yazidta/Flying-Probe-Tester/STM32/Components/Inc/encoder_config.h

/*
 * encoder_config.h
 *
 *  Created on: Nov 28, 2024
 *      Author: yazed
 */
/* Includes ------------------------------------------------------------------*/
#ifndef INC_ENCODER_CONFIG_H_
#define INC_ENCODER_CONFIG_H_

/* Config --------------------------------------------------------------------*/

/* Includes ------------------------------------------------------------------*/
#include "encoder.h"

/* Typedef -------------------------------------------------------------------*/

/* Define --------------------------------------------------------------------*/
extern TIM_HandleTypeDef htim4;
;

/* Macro ---------------------------------------------------------------------*/

/* Public variables ----------------------------------------------------------*/
extern ENC_Handle_TypeDef henc1;

/* Public function prototypes ------------------------------------------------*/

#endif /* INC_ENCODER_CONFIG_H_ */
