yazidta/Flying-Probe-Tester/STM32/Components/Inc/TMC2209.h

/******************************************************************************
 * @file       TMC2209.cpp
 * @author     Ahmed Bouras
 * @date       05/12/2024
 * @version    0.6
 *
 * @copyright  Copyright (c) [2024] Ahmed Bouras
 *
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
 * @note       This library provides an interface for controlling the TMC2209
 *             stepper motor driver over STEP, DIR, ENN & UART.
 ******************************************************************************
 */

#ifndef TMC2209_H
#define TMC2209_H

#include "stm32f7xx_hal.h"
#include "TMC2209_configs.h"
#include "TMC2209_register.h"
#include "extras.h"
#include "main.h"
#include "uart_handler.h"
#include <stdio.h>
#include <stdlib.h>
#include <string.h>
#include <stdbool.h>





// Datagrams
#define TMC_WRITE_DATAGRAM_SIZE  		8
#define TMC_READ_REQUEST_DATAGRAM_SIZE  4

// Macros & other
#define ENABLE_DEBUG					0		// If this is set to 1 then UART debug will be enabled
#define SYNC 							0x05     // Sync byte value for communication
#define SENDDELAY_MULTIPLIER 			8 		// 8-bit times per SENDDELAY unit
#define BAUD_RATE 						115200
#define TMC_ERROR						-1
#define TMC_ENABLESTALL_ERROR			10
#define TMC_STALL_ERROR					15
#define TMC_SEND_ERROR					20
#define TMC_NOREPLY_ERROR				30
#define TMC_SYNC_REPLY_ERROR			40
#define TMC_MCU_REPLY_ERROR				50
#define TMC_REG_REPLY_ERROR				60
#define TMC_CRC_REPLY_ERROR				70
#define TMC_IFCNT_ERROR					-80
#define TMC_GCONF_ERROR					90
#define TMC_IHOLD_ERROR					91
#define TMC_IRUN_ERROR					92
#define TMC_IDELAY_ERROR				93
#define TMC_SPREADCYCLE_ERROR1			95
#define TMC_SPREADCYCLE_ERROR2			100
#define TMC_SET_SPREADCYCLE_ERROR		105
#define TMC_SET_MSTEP_ERROR				110
#define TMC2209_IRUN_ERROR				120
#define TMC2209_SENDELAY_ERROR			130
#define TMC2209_TCOOLTHRS_ERROR			-10

#define TMC_OK							0






// Variables

extern uint32_t last_tmc_read_attempt_ms;
extern Axis axes[MAX_MOTORS_PER_AXIS];

// Function prototypes

void TMC2209_SetDirection(Motor *motor, GPIO_PinState state);
void TMC2209_EnableDriver(Motor *motor, GPIO_PinState state);
uint8_t TMC2209_ReadDiag(Motor *motor);
uint32_t TMC2209_ReadIndexStatus(Motor *motor);
void TMC2209_SetSpeed(Motor *motor, uint32_t StepFrequency);
void TMC2209_Step(Motor *motor, uint32_t steps);
void TMC2209_Stop(Motor *motor);
void TMC2209_Start(Motor *motor);
void TMC2209_checkStatus(Motor *motor, bool *isStepping, uint32_t *nextTotalSteps);
void TMC2209_MoveTo(Axis *axis, uint8_t motorIndex, float targetPositionMM);

uint8_t getStepPerUnit(Motor *motor);

//// UART TMC2209 ////
uint8_t calculate_CRC(uint8_t *datagram, uint8_t length);
uint8_t *TMC2209_sendCommand(uint8_t *command, size_t writeLength, size_t readLength, Motor *tmc2209);
void TMC2209_writeInit(Motor *tmc2209, uint8_t regAddress, int32_t value);
int32_t TMC2209_readInit(Motor *tmc2209, uint8_t regAddress);
uint8_t TMC2209_waitForReply(uint32_t timeout);

//// TMC2209 configuration functions (UART)  ////
bool TMC2209_setPDNuart(Motor *tmc2209, bool enable);
bool configureGCONF(Motor *tmc2209);
void TMC2209_read_ifcnt(Motor *tmc2209);
float TMC2209_readTemperature(Motor *tmc2209);
uint8_t TMC2209_enableStallDetection(Motor *tmc2209, uint8_t sgthrs);
void TMC2209_checkStall(Motor *tmc2209);
bool TMC2209_readStandstillIndicator(Motor *tmc2209);

uint32_t TMC2209_setMicrosteppingResolution(Motor *tmc2209, uint16_t resolution);
void checkMicrosteppingResolution(Motor *tmc2209);
uint16_t TMC2209_setSpreadCycle(Motor *motor, uint8_t enable);
void checkSpreadCycle(Motor *tmc2209);
uint16_t TMC2209_setIRUN(Motor *tmc2209, uint8_t irun_value);
void TMC2209_readIRUN(Motor *tmc2209);
void TMC2209_configureCurrent(Motor *tmc2209, uint8_t ihold, uint8_t irun, uint8_t iholddelay);
void TMC2209_SetTCoolThrs(Motor *tmc2209, uint32_t stepFrequency);

void TMC2209_setMotorsConfiguration(Motor *motors);
void TMC2209_resetMotorsConfiguration(Motor *motors);



//// Debug ////
void debug_print(const char* msg);
void debug_print_hex(uint8_t* data, uint8_t length);
void clear_UART_buffers(UART_HandleTypeDef *huart);
void TMC2209_MoveAllMotorsTo(Axis axes[2], float targetPositions[4]);



#endif // TMC2209_H
