yazidta/Flying-Probe-Tester/STM32/Components/Inc/LCD.h

#ifndef INC_LCD_H_
#define INC_LCD_H_

/* Config --------------------------------------------------------------------*/
#define LCD_PRINTF_ENABLE
#define LCD_USE_TIMER
#define MAX_LINES       500    // Maximum number of lines to process
#define LINE_BUFFER_SIZE 500
#define MAX_LINE_LENGTH 64
//#define LCD20xN    // For 20xN LCDs
#define LCD16xN     // For 16xN LCDs

#ifdef LCD16xN
#define LCD_LINE_LEN 16
#define LCD_LINE_BUF_LEN 17
#else
#define LCD_LINE_LEN 20
#define LCD_LINE_BUF_LEN 21
#endif
extern char lines[MAX_LINES][MAX_LINE_LENGTH];


/* Includes ------------------------------------------------------------------*/

#include <string.h>
#include <stdio.h>
#include "stm32f7xx_hal.h"
#include "encoder.h"
#include <stdbool.h>
#include "stm32f7xx_hal_tim.h"
#include "main.h"
#include "stm32f7xx_hal_conf.h"
#include <stdarg.h>
#include "sd_card_reader.h"
//#include "calibration.h"
/* Typedef -------------------------------------------------------------------*/
#define LCD_TimerType TIM_HandleTypeDef*

#define LCD_I2CType I2C_HandleTypeDef*

typedef struct {
  LCD_I2CType I2C;
  uint16_t Address;
  uint32_t Timeout;
  //LCD_ModeTypeDef Mode;
  LCD_TimerType Timer;
  _Bool IsInitialized;
} LCD_I2C_HandleTypeDef;

/* Define --------------------------------------------------------------------*/

#define LCD_CLEAR_DISPLAY 0x01

#define LCD_RETURN_HOME 0x02

#define LCD_ENTRY_MODE_SET 0x04
#define LCD_OPT_S   0x01        // Shift entire display to right
#define LCD_OPT_INC 0x02        // Cursor increment

#define LCD_DISPLAY_ON_OFF_CONTROL 0x08
#define LCD_OPT_D  0x04         // Turn on display
#define LCD_OPT_C  0x02         // Turn on cursor
#define LCD_OPT_B  0x01         // Turn on cursor blink

#define LCD_CURSOR_DISPLAY_SHIFT 0x10 // Move and shift cursor
#define LCD_OPT_SC 0x08
#define LCD_OPT_RL 0x04

#define LCD_FUNCTION_SET    0x20
#define LCD_OPT_DL          0x10    // Set interface data length
#define LCD_OPT_N           0x08    // Set number of display lines
#define LCD_OPT_F           0x04    // Set alternate font
#define LCD_SETCGRAM_ADDR  0x040
#define LCD_SET_DDRAM_ADDR  0x80    // Set DDRAM address

#define LCD_NIB  4
#define LCD_BYTE 8

#define LCD_DATA_REG    1
#define LCD_COMMAND_REG 0

#define LCD_MENU_CURSOR_CHAR 0x7E // '->' (ROM Code: A00)
#define LCD_I2C_BIT_RS                 0x01
#define LCD_I2C_BIT_RW                 0x02
#define LCD_I2C_BIT_E                  0x04
#define LCD_I2C_BIT_BACKIGHT_ON        0x08
#define LCD_I2C_BIT_BACKIGHT_OFF       0x00
#define MAX_FILES 10
#define LCD_ROWS 4
//#define LCD_WIDTH 20

/**
 * @brief LCD initialization procedure.
 * @note Cursor off, Cursor increment on, No blink @see HD44780 technical note.
 * @param[in] hlcd : LCD handler with I2C interface
 * @return None
 */
void LCD_I2C_Init(LCD_I2C_HandleTypeDef* hlcd);

/**
 * @brief Write a decimal number on the current position.
 * @param[in] hlcd   : LCD handler with I2C interface
 * @param[in] number : Decimal number
 * @return None
 */
void LCD_I2C_printDecInt(LCD_I2C_HandleTypeDef* hlcd, int number);

/**
 * @brief Write a hexadecimal number on the current position.
 * @param[in] hlcd   : LCD handler with I2C interface
 * @param[in] number : Hexadecimal number
 * @return None
 */
void LCD_I2C_printHexInt(LCD_I2C_HandleTypeDef* hlcd, int number);

/**
 * @brief Write a string on the current position.
 * @param[in] hlcd : LCD handler with I2C interface
 * @param[in] str  : Null-terminated string
 * @return None
 */
void LCD_I2C_printStr(LCD_I2C_HandleTypeDef* hlcd, char* str);

/**
 * @brief Set the cursor position.
 * @param[in] hlcd : LCD handler with I2C interface
 * @param[in] row  : Display row (line): 0 to N
 * @param[in] col  : Display column: 0 to 15 (16 character display) or 19 (20 character display)
 * @return None
 */
void LCD_I2C_SetCursor(LCD_I2C_HandleTypeDef* hlcd, uint8_t row, uint8_t col);

/**
 * @brief Clear the screen.
 * @param[in] hlcd : LCD handler with I2C interface
 * @return None
 */
void LCD_I2C_Clear(LCD_I2C_HandleTypeDef * lcd);

/**
 * @brief Write new character to display memory.
 * @param[in] hlcd   : LCD handler with I2C interface
 * @param[in] code   : Defined character code in display memory @see HD44780 technical note.
 * @param[in] bitmap : Defined character array @see HD44780 technical note.
 * @return None
 */
void LCD_I2C_DefineChar(LCD_I2C_HandleTypeDef* lcd, uint8_t code, uint8_t bitmap[]);

#ifdef LCD_PRINTF_ENABLE
/**
 * @brief Write text in standard format on the current position.
 * @param[in] hlcd   : LCD handler with I2C interface
 * @param[in] format : Text format @see http://www.cplusplus.com/reference/cstdio/printf/
 * @param[in] ...    : Variadic arguments
 * @return None
 */
void LCD_I2C_printf(LCD_I2C_HandleTypeDef* lcd, const char* format, ...);

void DisplaySequentialGlossyText(LCD_I2C_HandleTypeDef* hlcd, uint8_t row);
void DisplayGlossyText(LCD_I2C_HandleTypeDef* hlcd, uint8_t row);
void LCD_I2C_HandleMenuSelection(uint8_t selectedOption, LCD_I2C_HandleTypeDef* hlcd,ENC_Handle_TypeDef* henc);
void LCD_I2C_DisplayGlossyText(LCD_I2C_HandleTypeDef* hlcd, uint8_t row);
bool read_buttons(void);
uint8_t LCD_I2C_MainMenu_Encoder(LCD_I2C_HandleTypeDef* hlcd, ENC_Handle_TypeDef* henc);
void sd_card_display_files(LCD_I2C_HandleTypeDef* hlcd);
void LCD_I2C_DisplaySDMenu(LCD_I2C_HandleTypeDef* hlcd, ENC_Handle_TypeDef* henc);
void LCD_I2C_Cursor(LCD_I2C_HandleTypeDef* hlcd, uint8_t row, uint8_t col);
void DisplayMenu(LCD_I2C_HandleTypeDef* hlcd, char fileList[][20 + 1], uint8_t fileCount, uint8_t selectedIndex);
void AddBackOption(char fileList[][20 + 1], uint8_t index);
uint8_t LCD_I2C_menuTemplate(LCD_I2C_HandleTypeDef* hlcd,
                             ENC_Handle_TypeDef* henc,
                             const char* displayItems[],
                             uint8_t numItems,
                             bool backOption);
uint8_t ReadFiles(DIR* dir, char fileList[][20 + 1], uint8_t maxFiles);
FRESULT OpenRootDir(DIR* dir);
FRESULT MountSDCard(FATFS* FatFs);
void LCD_I2C_ClearAllLines(LCD_I2C_HandleTypeDef * hlcd);
void generate_report(LCD_I2C_HandleTypeDef* hlcd);



#endif

#endif /* INC_LCD_H_ */
