yazidta/Flying-Probe-Tester/STM32/Components/Inc/command_parser.h

/*
 * command_parser.h
 *
 *  Created on: Jan 16, 2025
 *      Author: ahmed
 */

#ifndef INC_COMMAND_PARSER_H_
#define INC_COMMAND_PARSER_H_

void parsePCB2GcodeCommand(char *command);

#endif /* INC_COMMAND_PARSER_H_ */
