yazidta/Flying-Probe-Tester/STM32/Components/Src/lcd_config.c

/**
  ******************************************************************************
  * @file    lcd_config.c
  * @author  Konrad Marchewka
  * @author   : AW    Adrian.Wojcik@put.poznan.pl
  * @version V1.0
  * @date    23-Jan-2024
  * @brief   Simple HD44780 driver library for STM32F7 configuration file.
  *
  ******************************************************************************
  */
  /* Private includes ----------------------------------------------------------*/

#include "LCD.h"
#include "lcd_config.h"
#include "main.h"
#include "stm32f7xx_hal_i2c.h"
#include "stm32f7xx_hal_tim.h"

//#include "i2c.h"
//#include "tim.h"

/* Private typedef -----------------------------------------------------------*/

/* Private define ------------------------------------------------------------*/
#ifdef LCD_USE_TIMER
#endif
/* Private macro -------------------------------------------------------------*/

/* Private variables ---------------------------------------------------------*/

/* Public variables ----------------------------------------------------------*/
extern I2C_HandleTypeDef hi2c1;
extern TIM_HandleTypeDef htim7;

LCD_I2C_HandleTypeDef hlcd3 = {
    .I2C = &hi2c1,
    .Address = 0x27,  // PCF8574T (for all jumpers OPEN)
    .Timeout = 100,
    .Timer = &htim7
};

/* Private function prototypes -----------------------------------------------*/

/* Public function prototypes ------------------------------------------------*/

/* Private functions ---------------------------------------------------------*/

/* Public functions ----------------------------------------------------------*/
